Rocketdude1984/EchoWeather/Parts/Main/Prints/EchoWeather_StevensonScreen_Ring.stl

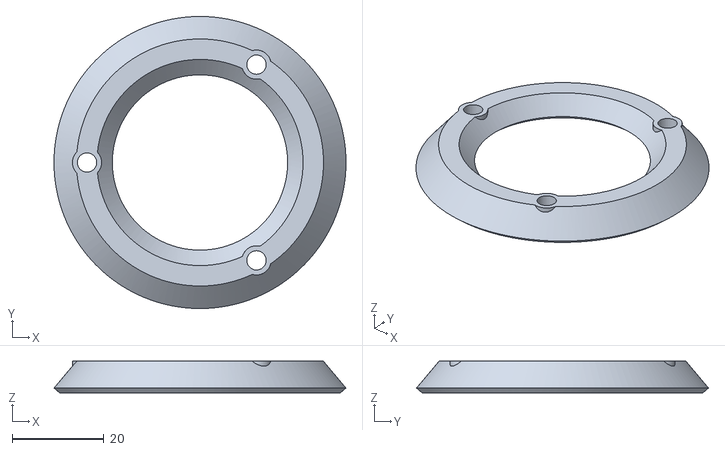
[picture p24: CAD file, 2025-09-13]
Parts/Main/Prints/EchoWeather_StevensonScreen_Ring.stl
63.5 x 63.5 x 6.86
