Rocketdude1984/EchoWeather/Parts/RainGauge/Prints/EchoWeather_RainGauge_Funnel.stl

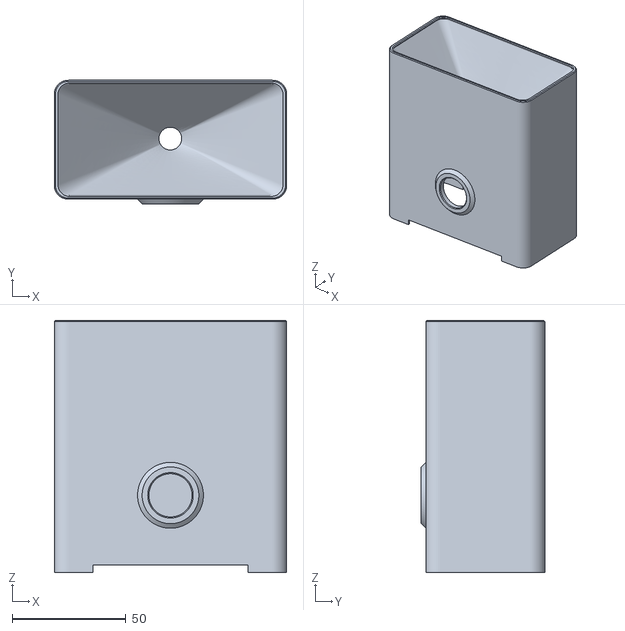
[picture p25: CAD file, 2025-11-03]
Parts/RainGauge/Prints/EchoWeather_RainGauge_Funnel.stl
102.4 x 54.4 x 111.0
