Rocketdude1984/EchoWeather/Parts/Support Rod/Prints/EchoWeather_InnerClamp.stl

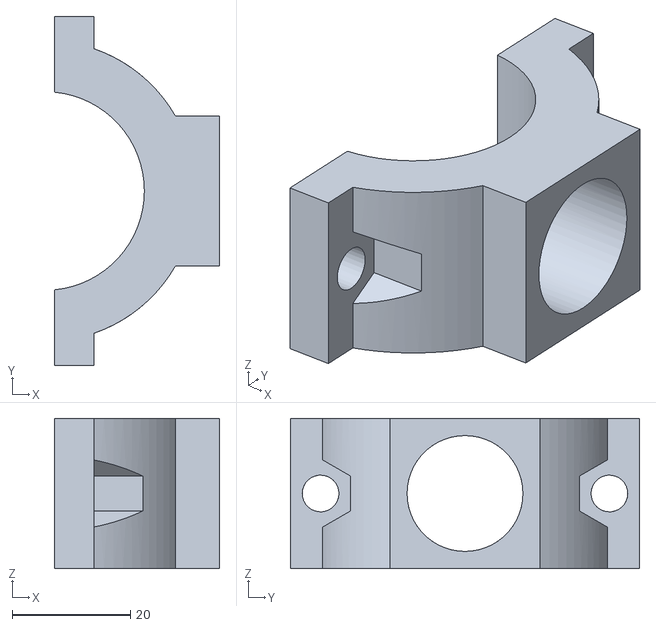
[picture p26: CAD file, 2025-09-13]
Parts/Support Rod/Prints/EchoWeather_InnerClamp.stl
27.9 x 58.9 x 25.4
