Rocketdude1984/EchoWeather/Parts/Windvane/WindVane_Prints/EchoWeather_WindVane_InnerRotor.stl

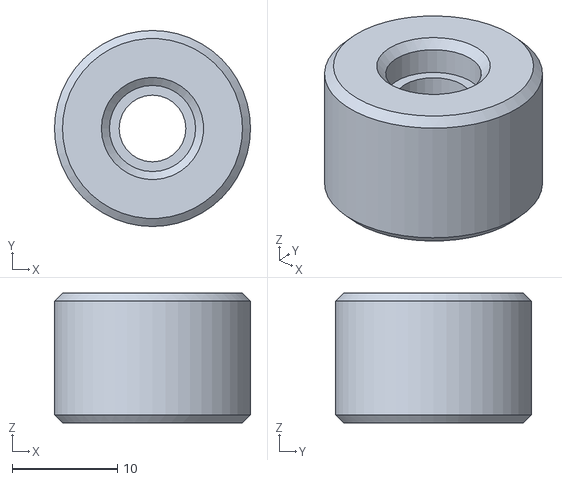
[picture p27: CAD file, 2025-09-13]
Parts/Windvane/WindVane_Prints/EchoWeather_WindVane_InnerRotor.stl
18.6 x 18.6 x 12.3
