Rocketdude1984/EchoWeather/Parts/RainGauge/Prints/EchoWeather_RainGauge_BottomGrid.stl

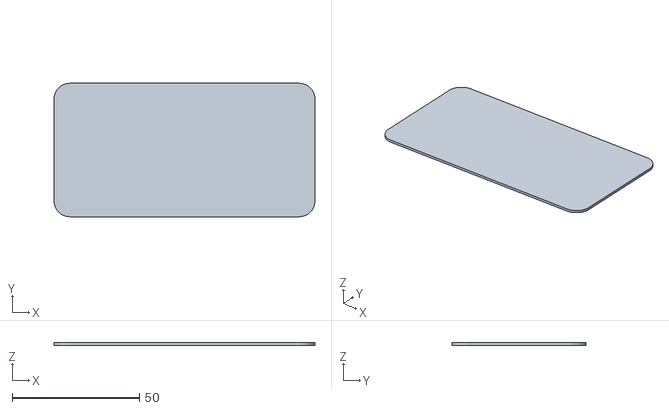
[picture p28: CAD file, 2025-11-03]
Parts/RainGauge/Prints/EchoWeather_RainGauge_BottomGrid.stl
102.4 x 52.4 x 1.00
