Rocketdude1984/EchoWeather/Parts/Windvane/WindVane_Prints/EchoWeather_WindVane_Enclosure.stl

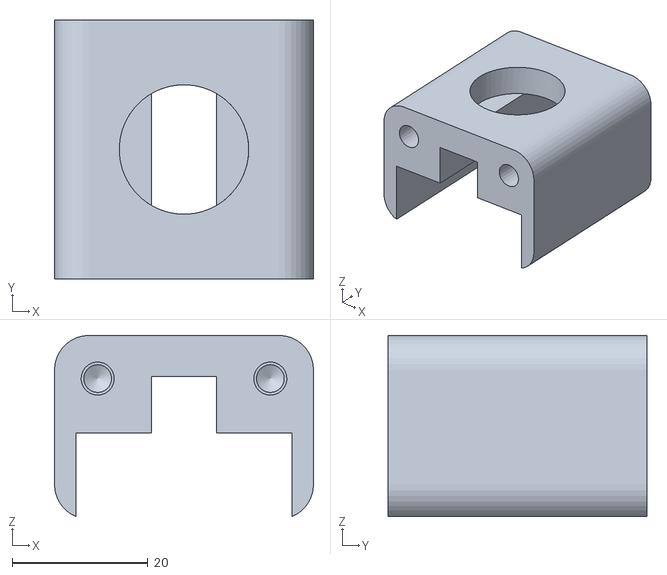
[picture p29: CAD file, 2025-09-13]
Parts/Windvane/WindVane_Prints/EchoWeather_WindVane_Enclosure.stl
38.1 x 38.1 x 26.7
