Rocketdude1984/EchoWeather/Parts/RainGauge/Prints/EchoWeather_RainGauge_Fulcrum.stl

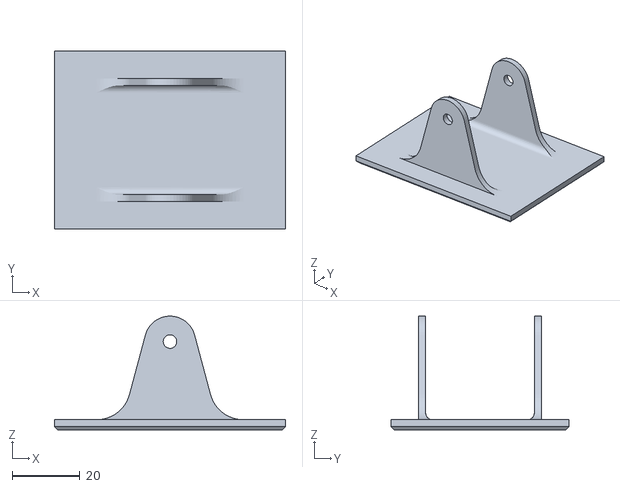
[picture p30: CAD file, 2025-11-03]
Parts/RainGauge/Prints/EchoWeather_RainGauge_Fulcrum.stl
68.0 x 52.4 x 33.5
