Rocketdude1984/EchoWeather/Parts/Windvane/WindVane_Prints/EchoWeather_WindVane_Vane.stl

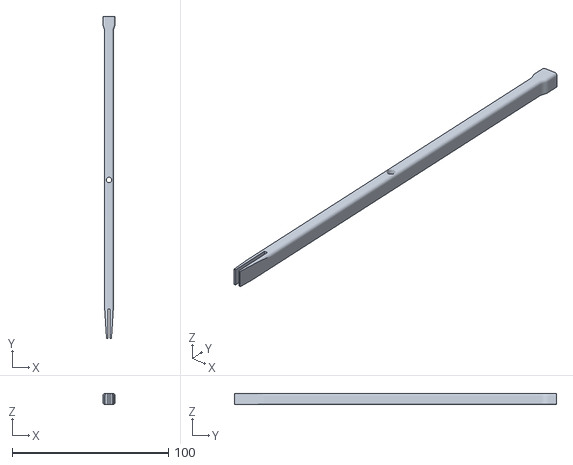
[picture p31: CAD file, 2025-09-13]
Parts/Windvane/WindVane_Prints/EchoWeather_WindVane_Vane.stl
7.62 x 206.4 x 7.11
