Rocketdude1984/EchoWeather/Parts/Windvane/WindVane_Prints/EchoWeather_WindVane_Shaft.stl

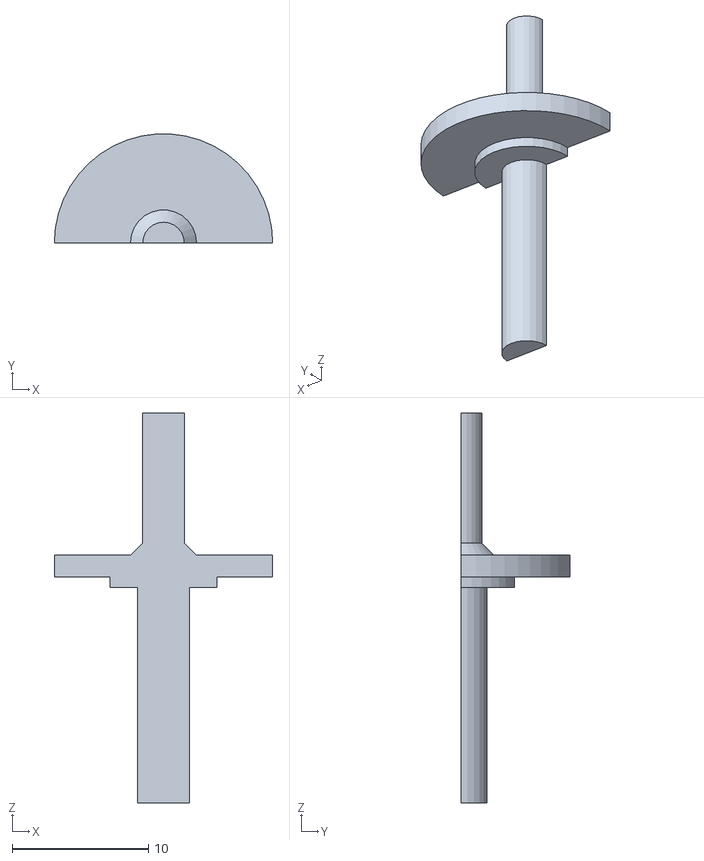
[picture p32: CAD file, 2025-09-13]
Parts/Windvane/WindVane_Prints/EchoWeather_WindVane_Shaft.stl
16.0 x 7.98 x 28.6
