Rocketdude1984/EchoWeather/Parts/Main/Prints/EchoWeather_StevensonScreen_Bottom.stl

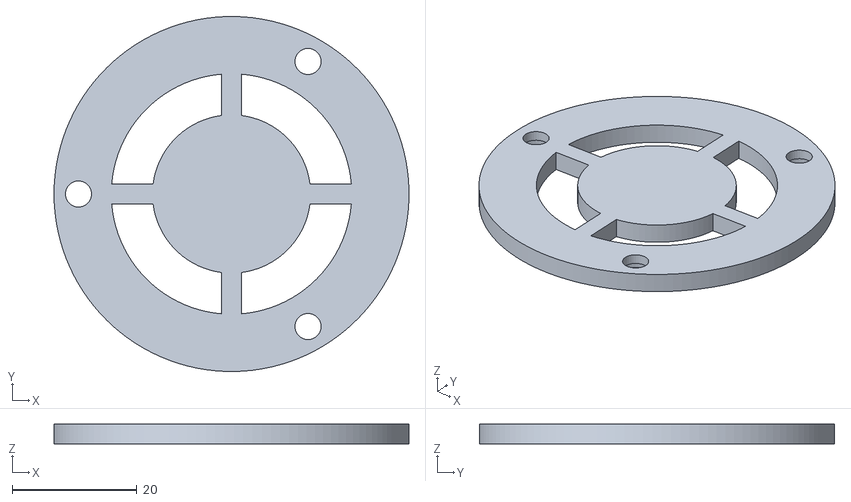
[picture p33: CAD file, 2025-09-13]
Parts/Main/Prints/EchoWeather_StevensonScreen_Bottom.stl
57.0 x 57.0 x 3.18
