Rocketdude1984/EchoWeather/Parts/Windvane/WindVane_Prints/EchoWeather_WindVane_Tail.stl

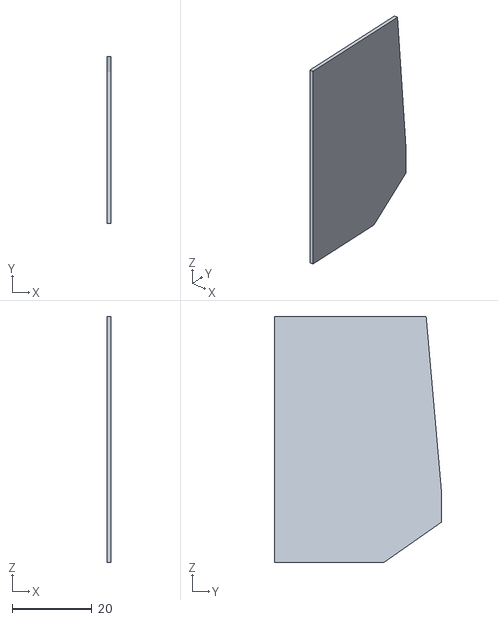
[picture p34: CAD file, 2025-09-13]
Parts/Windvane/WindVane_Prints/EchoWeather_WindVane_Tail.stl
1.12 x 42.0 x 61.7
