Rocketdude1984/EchoWeather/Parts/Main/Prints/EchoWeather_StevensonScreen_MountingPlate.stl

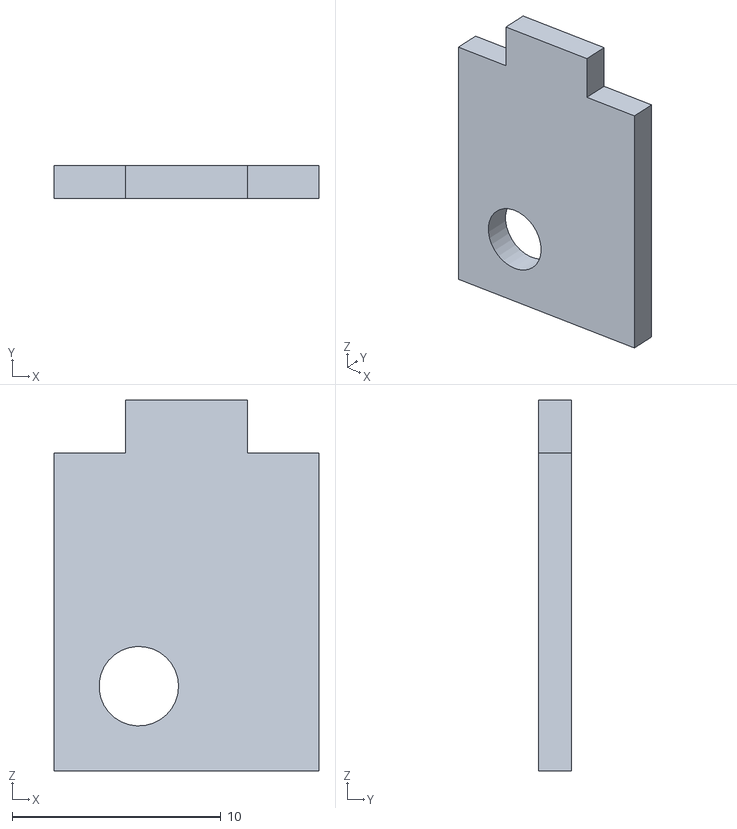
[picture p36: CAD file, 2025-09-13]
Parts/Main/Prints/EchoWeather_StevensonScreen_MountingPlate.stl
12.7 x 1.59 x 17.8
