Rocketdude1984/EchoWeather/Parts/Main/Prints/EchoWeather_StevensonScreen_Lid.stl

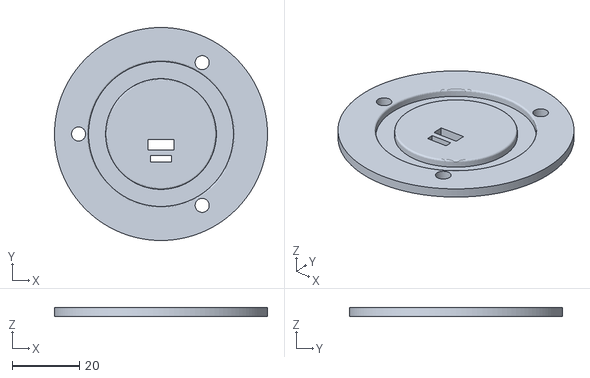
[picture p38: CAD file, 2025-09-13]
Parts/Main/Prints/EchoWeather_StevensonScreen_Lid.stl
63.5 x 63.5 x 2.54
